RbtsEvrwhr-Riley/CellSol/website/content/about-cellsol/cellsolteam/riley.md

---
title: Riley August
weight: -9
publishdate: 2019-11-17
lastmod: 2020-11-24
---

Riley is the current project manager for the CellSol project, and one of the co-founders of [Robots Everywhere](https://www.robots-everywhere.com), along with Kay Borri. Riley is an experienced software
architect, project manager, and test planner. Outside of software automation, Riley's skills are quite diverse, from 3D modeling and CAD to logic simulations and rules modeling. Riley has made contributions
all across the CellSol project, and even designed this website.

Outside of the shop, Riley likes to ride his bicycle, and test his skills against the world in online games like League of Legends.

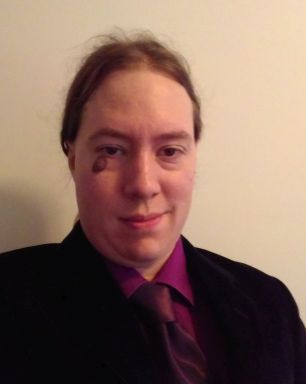
[picture p4: website/content/about-cellsol/cellsolteam/riley_profile.jpg]
Riley August, unusually wearing a suit
