RbtsEvrwhr-Riley/CellSol/website/content/cellsol-equipment/arduino/_index.md

---
title: Arduino Repeater Pylon
publishdate: 2019-11-17
lastmod: 2020-11-24
---

The Arduino Repeater Pylon is a low cost CellSol pylon designed for mass deployment. While it can only be accessed from a single other device using a Bluetooth
pairing, its main function is to forward messages along the network, extending the overall range for more complex pylons.

In the future, a repeater-router pylon may act as an upgrade for this model, allowing for multiple networks to interconnect.

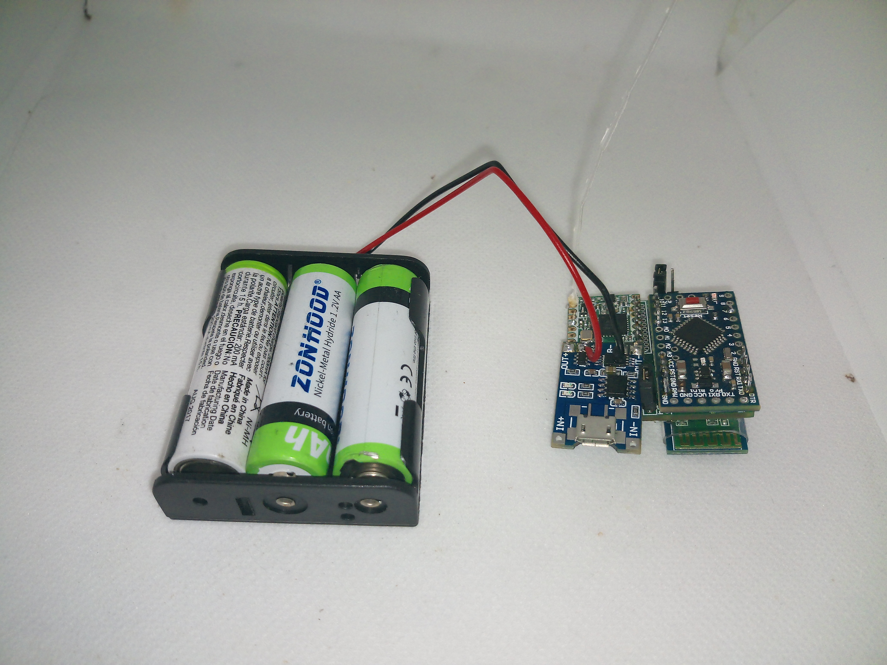
[picture p5: website/content/cellsol-equipment/arduino/arduino_pylon_nocase.jpg]
A CellSol Arduino Repeater Pylon, Built with No Case
