RbtsEvrwhr-Riley/CellSol/website/content/cellsol-equipment/esp32/_index.md

---
title: ESP32 WiFi Pylon
publishdate: 2019-11-17
lastmod: 2020-11-24
---

The ESP32 WiFi Pylon is an easy to assemble, WiFi capable CellSol pylon. It can be set up as its own WiFi access point, or connect to existing WiFi networks,
and serves a simple proof-of-concept chat app that broadcasts along the LoRa network.

It uses the Heltec Lora32 or Lora32V2 microcontroller board as its base.

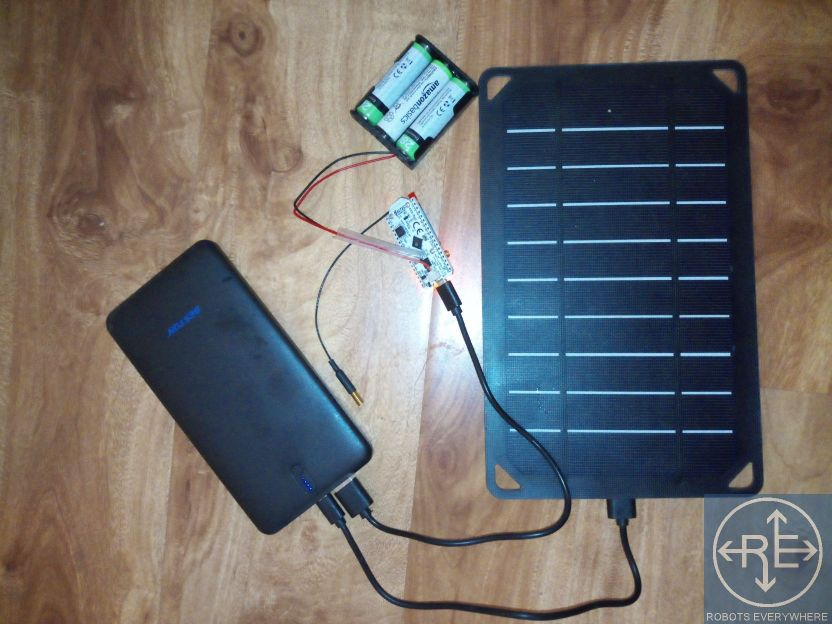
[picture p6: website/content/cellsol-equipment/esp32/esp32pylon_assembled.jpg]
A CellSol ESP32 WiFi Pylon, Assembled, No Case
