RbtsEvrwhr-Riley/CellSol/website/content/about-cellsol/cellsolteam/robotseverywhere.md

---
title: Robots Everywhere, LLC
publishdate: 2019-11-17
lastmod: 2020-11-24

---

Robots Everywhere was founded by Kay Borri and Riley August as a robotics consulting firm in 2008. Since then, they have developed many navigation, instrumentation, robotics, 
and manufacturing solutions for the public and private sectors, as well as the maker community. The company has always believed in doing the best for humanity, and with
the many crises plaguing the year 2020, Robots Everywhere has chosen this time to help develop launch CellSol to allow people to come together in the future.

They can be found at [www.robots-everywhere.com](https://www.robots-everywhere.com).

Robots Everywhere logo
