RbtsEvrwhr-Riley/CellSol/esp32/esp32_wifi_bt/btt/cat.jpg

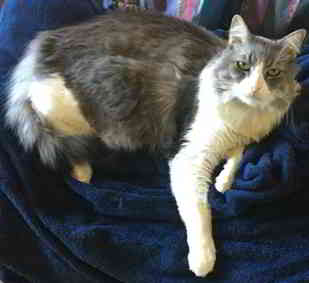
esp32/esp32_wifi_bt/btt/cat.jpg
