RbtsEvrwhr-Riley/CellSol/help_graphic.png

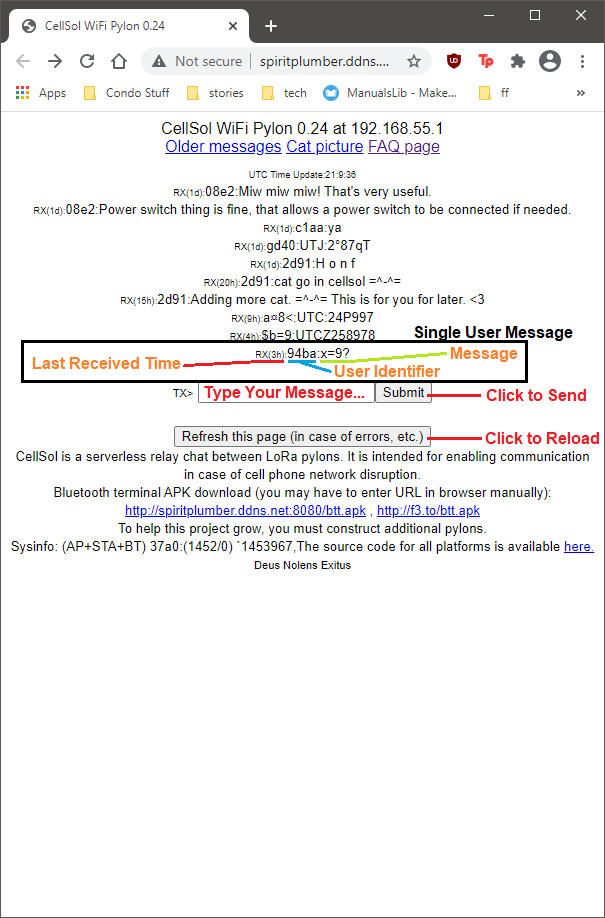
help_graphic.png
