RbtsEvrwhr-Riley/CellSol/help_graphic_small.jpg

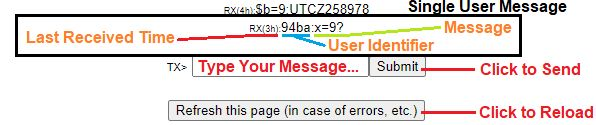
help_graphic_small.jpg
