RbtsEvrwhr-Riley/CellSol/nano/photos/IMG_20201117_164300_0.jpg

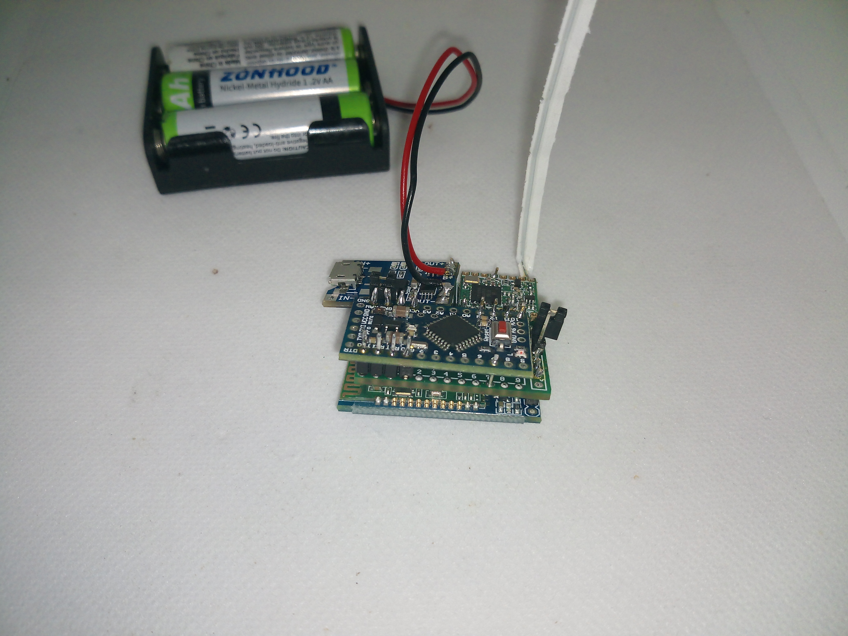
nano/photos/IMG_20201117_164300_0.jpg
