RbtsEvrwhr-Riley/CellSol/nano/photos/IMG_20201117_164333_2.jpg

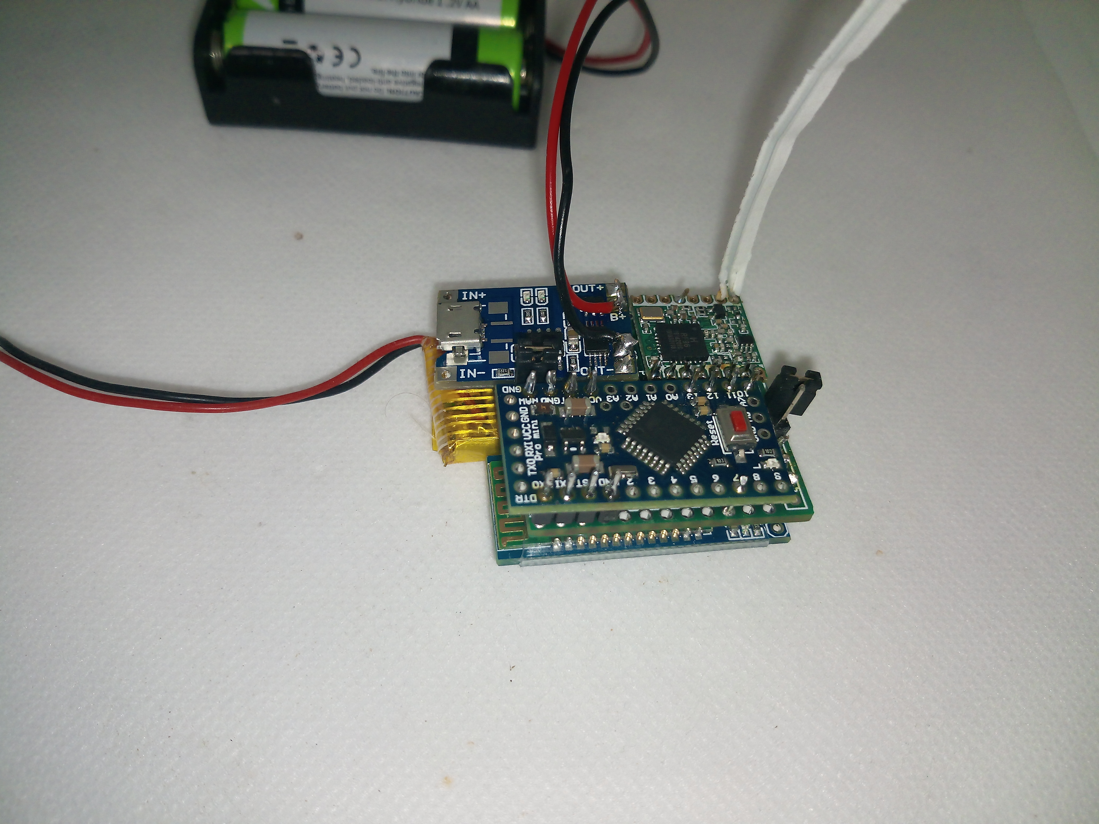
nano/photos/IMG_20201117_164333_2.jpg
