RbtsEvrwhr-Riley/CellSol/nano/photos/IMG_20201117_164346_4.jpg

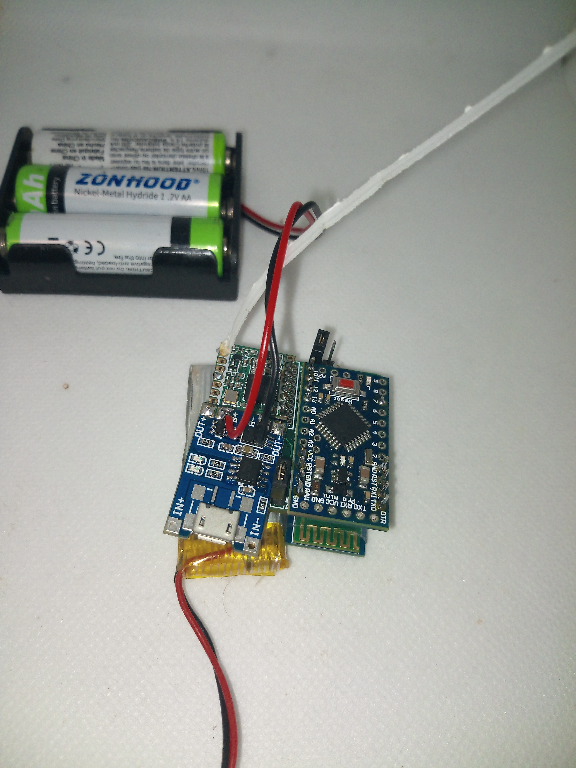
nano/photos/IMG_20201117_164346_4.jpg
