RbtsEvrwhr-Riley/CellSol/nano/photos/IMG_20201117_164406_4.jpg

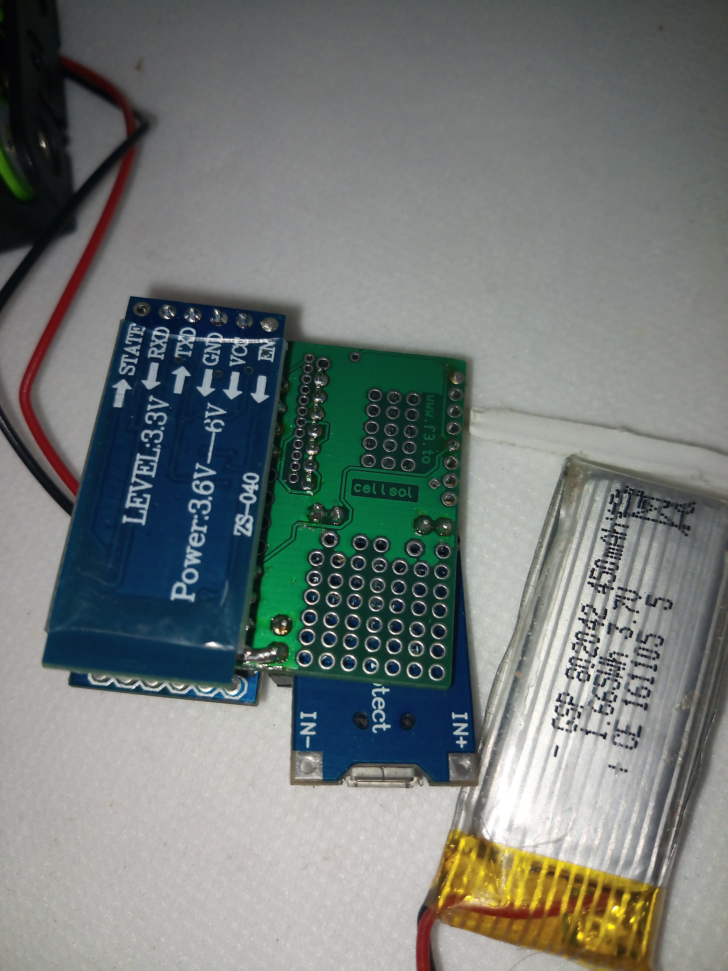
nano/photos/IMG_20201117_164406_4.jpg
