RbtsEvrwhr-Riley/CellSol/nano/photos/IMG_20201117_164420_5.jpg

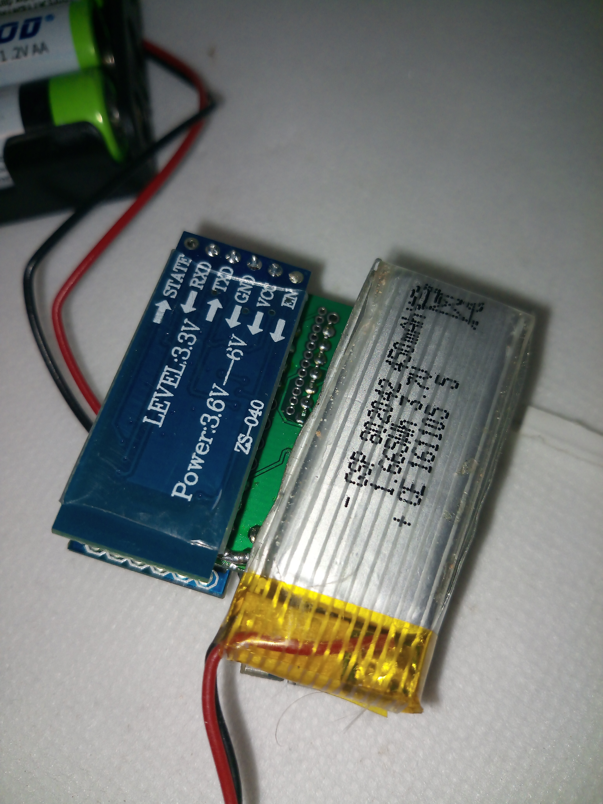
nano/photos/IMG_20201117_164420_5.jpg
