RbtsEvrwhr-Riley/CellSol/nano/photos/IMG_20201117_164456_1.jpg

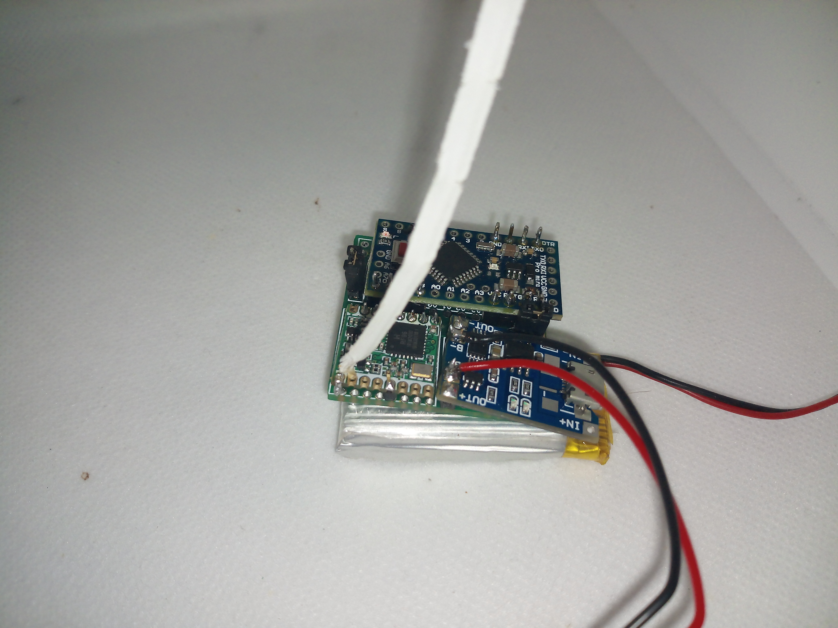
nano/photos/IMG_20201117_164456_1.jpg
