RbtsEvrwhr-Riley/CellSol/website/content/about-cellsol/photos/help_graphic.png

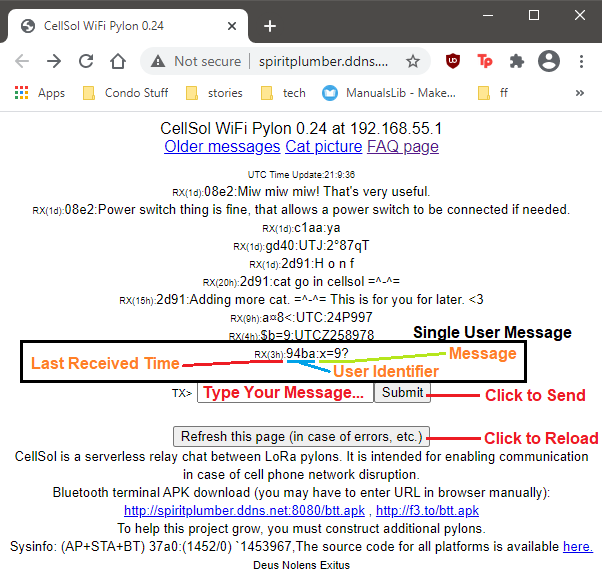
website/content/about-cellsol/photos/help_graphic.png
