RbtsEvrwhr-Riley/CellSol/website/content/cellsol-equipment/esp32/assembly-instructions/photos/fig1_boardmanagerurls.png

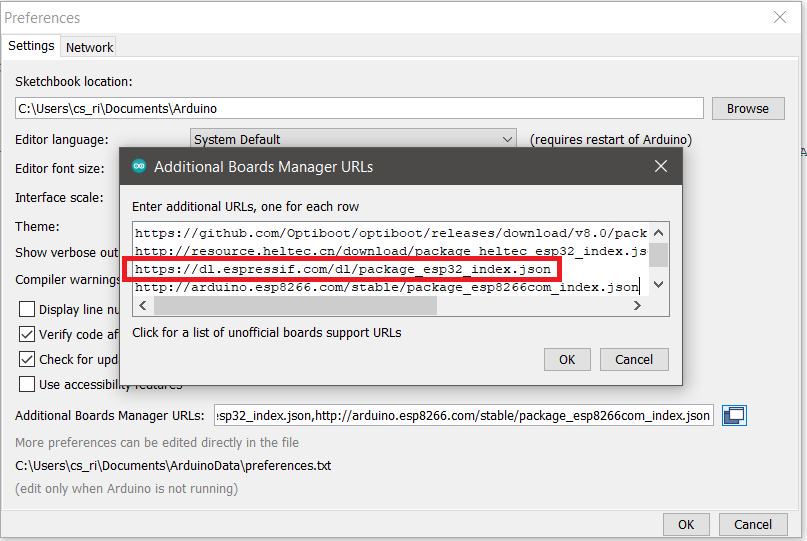
website/content/cellsol-equipment/esp32/assembly-instructions/photos/fig1_boardmanagerurls.png
