RbtsEvrwhr-Riley/CellSol/website/content/cellsol-equipment/esp32/assembly-instructions/photos/fig2_boardmanager.png

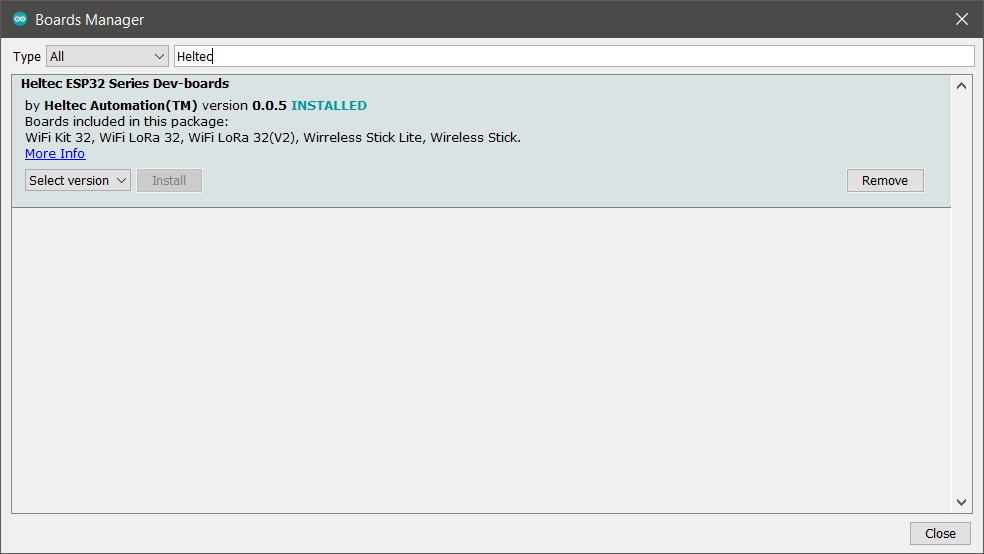
website/content/cellsol-equipment/esp32/assembly-instructions/photos/fig2_boardmanager.png
