RbtsEvrwhr-Riley/CellSol/website/content/cellsol-equipment/esp32/assembly-instructions/photos/fig3_librarymanager.png

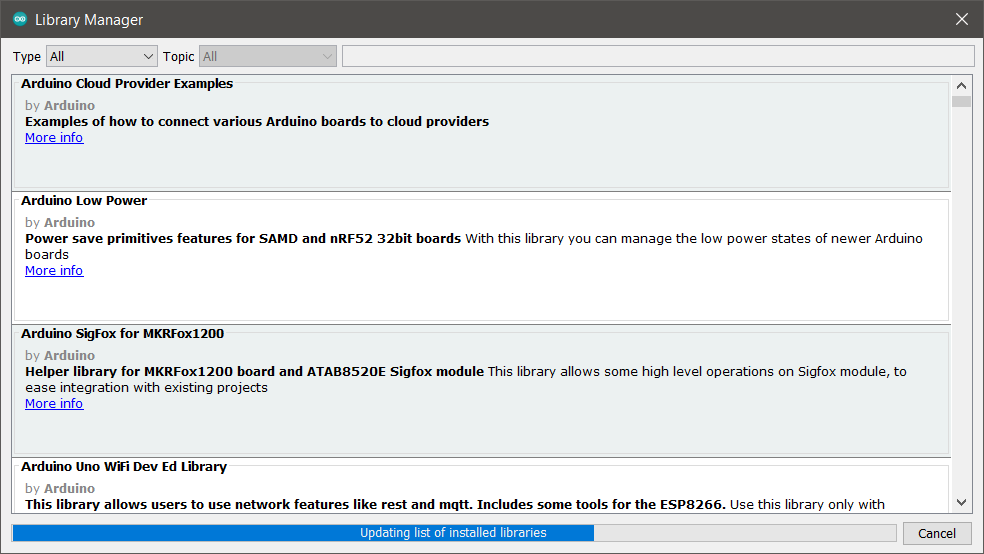
website/content/cellsol-equipment/esp32/assembly-instructions/photos/fig3_librarymanager.png
