RbtsEvrwhr-Riley/CellSol/website/content/cellsol-equipment/esp32/assembly-instructions/photos/fig5_selectlora32.png

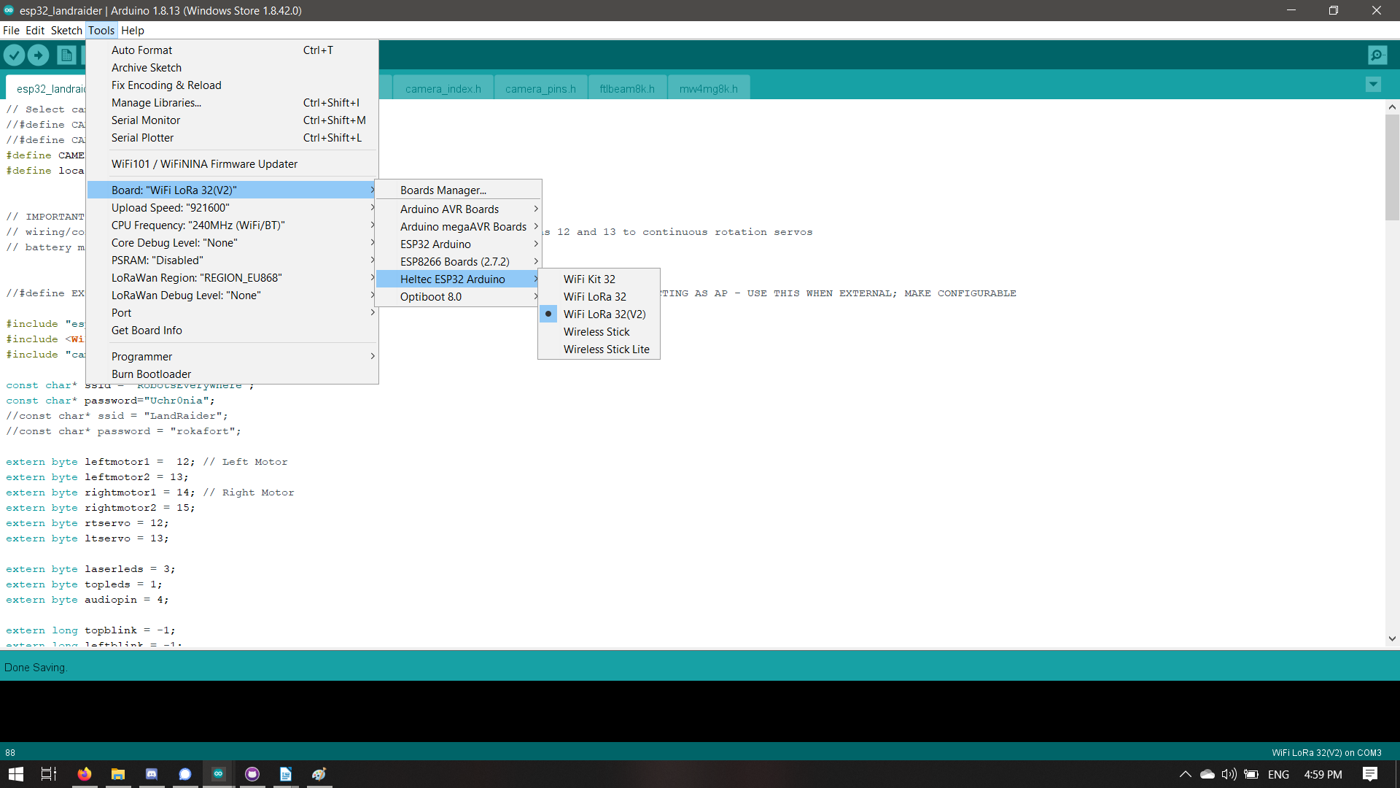
website/content/cellsol-equipment/esp32/assembly-instructions/photos/fig5_selectlora32.png
